grafisoft/SpainLabsIoT2018/SpainLabsIoT_ESPNode_Alfa_v2/src/funciones.h

// DECLARACION DE FUNCIONES Y LIBRERIAS NECESARIAS PARA EL PROYECTO.

#include <ESP8266WiFi.h>  //WIFI ESP8266
#include <PubSubClient.h>  // MQTT
#include <Wire.h>
#include <SPI.h>
#include <Adafruit_Sensor.h>
#include <Adafruit_BME280.h>

#define SEALEVELPRESSURE_HPA (1034.9)
Adafruit_BME280 bme; // I2C
//#define BME280_ADDRESS  0x77
unsigned long delayTime;

// Update these with values suitable for your network.
const char* ssid = "MOVISTAR_S3N0";
const char* password = "TestSensor2017";
const char* mqtt_server = "10.3.141.1";

WiFiClient espClient;
PubSubClient client(espClient);
long lastMsg = 0;
char msg[50];
int value = 0;

// Tiempo de deepsleep. Cambiando el primer parametro. La cuenta o convierte en uS.
const int sleeptime = 20 * 60 * 1000000;

// FUNCIONES.
void setup_wifi() {

  delay(10);
  // We start by connecting to a WiFi network
  Serial.println();
  Serial.print("Connecting to ");
  Serial.println(ssid);

  WiFi.begin(ssid, password);

  while (WiFi.status() != WL_CONNECTED) {
    delay(500);
    Serial.print(".");
  }

  Serial.println("");
  Serial.println("WiFi connected");
  Serial.println("IP address: ");
  Serial.println(WiFi.localIP());
}

void callback(char* topic, byte* payload, unsigned int length) {
  Serial.print("Message arrived [");
  Serial.print(topic);
  Serial.print("] ");
  for (int i = 0; i < length; i++) {
    Serial.print((char)payload[i]);
  }
  Serial.println();

}

void reconnect() {
  // Loop until we're reconnected
  while (!client.connected()) {
    Serial.print("Attempting MQTT connection...");
    // Attempt to connect
    if (client.connect("ESP8266Client")) {
      Serial.println("connected");
      // Once connected, publish an announcement...
      client.publish("outTopic", "hello world");
      // ... and resubscribe
      client.subscribe("inTopic");
    } else {
      Serial.print("failed, rc=");
      Serial.print(client.state());
      Serial.println(" try again in 5 seconds");
      // Wait 5 seconds before retrying
      delay(5000);
    }
  }
}

//Funcion para la lectura de los valores del sensor BME.
//Los valores tambien se imprimen por consola.
void leerbme(){
  Serial.print("Temperature = ");
  Serial.print(bme.readTemperature());
  Serial.println(" *C");

  Serial.print("Pressure = ");

  Serial.print(bme.readPressure() / 100.0F);
  Serial.println(" hPa");

  Serial.print("Approx. Altitude = ");
  Serial.print(bme.readAltitude(SEALEVELPRESSURE_HPA));
  Serial.println(" m");

  Serial.print("Humidity = ");
  Serial.print(bme.readHumidity());
  Serial.println(" %");

  Serial.println();
    delay(delayTime);
}
